rodneyknaap/atx-turboxt-v3/Turbo_XT_Mainboard R3.sch

## KiCad design Turbo_XT_Mainboard R3.sch (2023-07-02)

Schematic: Turbo_XT_Mainboard R3.sch

Parts:
C1: 50p; Trimmer_C
C2, C3: 12p; C_Disc_D3.8mm_W2.6mm_P2.50mm
C4: 100n; C_Disc_D5.0mm_W2.5mm_P5.00mm
C5, C6, C7: 1nF; C_Disc_D3.8mm_W2.6mm_P2.50mm
C8, C14, C15, C16, C17, C18, C30, C31, C32, C33, C34, C35, C36, C37, C38, C39, C40, C41, C42, C43, C44, C45, C46, C47, C48, C49, C50, C51, C52, C53, C54, C55, C56, C57, C58, C59, C60, C61, C62, C63, C64, C65, C66, C67, C68, C69, C70, C71, C72, C73, C74, C75, C76, C77, C78, C79, C80, C81, C82, C83, C84, C85, C89, C90, C91, C92, C93, C94, C95, C96, C97, C99, C151, C177, C179, C181, C183, C184, C186, C187: 100nF; C_Rect_L7.0mm_W2.0mm_P5.00mm
C9, C10, C87, C88: 22pF; C_Disc_D3.8mm_W2.6mm_P2.50mm
C11: 4,7uF; CP_Radial_D4.0mm_P2.00mm
C12, C13: 100nF; C_Disc_D4.7mm_W2.5mm_P5.00mm
C21, C22, C23, C24, C25, C26, C27, C28, C29: 2,2nF; C_Disc_D4.7mm_W2.5mm_P5.00mm
C86, C178, C180: 1000µF; CP_Radial_D10.0mm_P5.00mm
C98: 2n2; C_Disc_D3.8mm_W2.6mm_P2.50mm
C100, C152, C188: 100µF; CP_Radial_D8.0mm_P3.80mm
C101, C102, C103, C105, C106, C107, C108, C109, C110, C111, C112, C114, C115, C116, C117, C118, C119, C120, C121, C122, C123, C124, C125, C126, C127, C128, C129, C130, C131, C132, C133, C134, C135, C136, C137, C138, C139, C140, C141, C142, C143, C144, C145, C146, C147, C148, C149, C150, C155, C156, C157, C158, C159, C160, C161, C162, C163, C164, C165, C166, C167, C168, C169, C170, C171, C172, C173, C174, C175, C176: 470p; C_Disc_D3.8mm_W2.6mm_P2.50mm
C104: 150p; C_Disc_D3.8mm_W2.6mm_P2.50mm
C113: 100p; C_Disc_D3.8mm_W2.6mm_P2.50mm
C153, C154: 1n; C_Disc_D3.8mm_W2.6mm_P2.50mm
C182: 47pF; C_Rect_L7.0mm_W2.0mm_P5.00mm
C185: 10µF; CP_Radial_D6.3mm_P2.50mm
D1: 1N4148; D_DO-35_SOD27_P5.08mm_Horizontal
D2: LED; LED_D5.0mm
D4: 1N5819; D_DO-15_P10.16mm_Horizontal
F1: FUSE 8A; R_Axial_DIN0207_L6.3mm_D2.5mm_P10.16mm_Horizontal
F2: FUSE 5A; R_Axial_DIN0207_L6.3mm_D2.5mm_P10.16mm_Horizontal
F3: FUSE 1A; R_Axial_DIN0207_L6.3mm_D2.5mm_P10.16mm_Horizontal
FB1: Ferrite_Bead_Small; R_Axial_DIN0207_L6.3mm_D2.5mm_P10.16mm_Horizontal
H1, H2, H3, H4, H5, H6, H7, H8, H9, H10: MountingHole_Pad; MountingHole_4mm_Pad_Via
J1: SPEAKER; PinHeader_1x04_P2.54mm_Vertical
J2, J4, J15, J17, J19, J23, J24: Conn_01x02; PinHeader_1x02_P2.54mm_Vertical
J5: Conn_01x05_Shielded; DIN_5P_FEMALE_PCB
J6, J8, J9, J10, J11, J12, J13: ISA_16bit_Slot; PCB_edge_ISA_Slot
J14: ATX-24 PSU; Molex_Mini-Fit_Jr_5566-24A2_2x12_P4.20mm_Vertical
J18: Conn_02x17_Odd_Even; IDC-Header_2x17_P2.54mm_Vertical
J20: Conn_01x25_Shielded_LPT; DSUB-25_Female_Horizontal_P2.77x2.84mm_EdgePinOffset4.94mm_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
J21: IDE_BUS; IDC-Header_2x20_P2.54mm_Vertical
J22: HDD_ACT_LED; PinHeader_1x02_P2.54mm_Vertical
J25: Conn_01x09_Shielded; DSUB-9_Male_Horizontal_COMPORT
J28: RJ45_Hanrun_HR911105A
J30, J31, J32: Conn_01x03; PinHeader_1x03_P2.54mm_Vertical
J33: SCSI_ADDRESS; PinHeader_2x03_P2.54mm_Vertical
J36: SCSI_INTERNAL; IDC-Header_2x25_P2.54mm_Vertical
Q1: 2N4401; TO-92_Wide
R4, R32, R35, R38, R39, R40, R43, R44: 10k; R_Axial_DIN0207_L6.3mm_D2.5mm_P10.16mm_Horizontal
R8, R27, R30, R48, R49: 4k7; R_Axial_DIN0207_L6.3mm_D2.5mm_P10.16mm_Horizontal
R9, R10: 510; R_Axial_DIN0207_L6.3mm_D2.5mm_P10.16mm_Horizontal
R11, R25, R45: 10M; R_Axial_DIN0207_L6.3mm_D2.5mm_P10.16mm_Horizontal
R12: 270; R_Axial_DIN0207_L6.3mm_D2.5mm_P10.16mm_Horizontal
R14, R42: 1k; R_Axial_DIN0207_L6.3mm_D2.5mm_P10.16mm_Horizontal
R15: 10; R_Axial_DIN0207_L6.3mm_D2.5mm_P10.16mm_Horizontal
R16, R36: 470; R_Axial_DIN0207_L6.3mm_D2.5mm_P10.16mm_Horizontal
R19, R20, R21, R22, R23: 33; R_Axial_DIN0207_L6.3mm_D2.5mm_P10.16mm_Horizontal
R26, R46: 2k2; R_Axial_DIN0207_L6.3mm_D2.5mm_P10.16mm_Horizontal
R28, R31: 100k; R_Axial_DIN0207_L6.3mm_D2.5mm_P10.16mm_Horizontal
R50: 27k; R_Axial_DIN0207_L6.3mm_D2.5mm_P10.16mm_Horizontal
R51: 200; R_Axial_DIN0207_L6.3mm_D2.5mm_P10.16mm_Horizontal
R52, R53: 330; R_Axial_DIN0207_L6.3mm_D2.5mm_P10.16mm_Horizontal
R56, R58: 220; R_Axial_DIN0207_L6.3mm_D2.5mm_P7.62mm_Horizontal
R57, R59: 330; R_Axial_DIN0207_L6.3mm_D2.5mm_P7.62mm_Horizontal
RN1, RN2: 8x 4k7; R_Array_SIP9
RN3: 4x 4k7; R_Array_SIP5
RN4: 4k7 x 8; R_Array_SIP9
RN5: 1kx8; R_Array_SIP9
RN6: 4k7x8; R_Array_SIP9
RN7, RN9: 8x 220; R_Array_SIP9
RN8, RN10: 8x 330; R_Array_SIP9
RN11: 8x 10k; R_Array_SIP9
SW1: SW_DIP_x08; SW_DIP_SPSTx08_Slide_9.78x22.5mm_W7.62mm_P2.54mm
U1: D70108C-8 NEC V20; DIP-40_W15.24mm
U2, U4, U24, U74, U75: 74HCT573E TI; DIP-20_W7.62mm
U3, U5, U6, U7, U8, U9, U10, U17: 74LS245N TI; DIP-20_W7.62mm
U12: TMS27C010A TI; DIP-32_W15.24mm
U13, U14: K6T4008CTB; DIP-32_W15.24mm
U15: 8087; DIP-40_W15.24mm
U16: CP82C88 HARRIS; DIP-20_W7.62mm
U19: M82C84A-2 OKI; DIP-18_W7.62mm
U20: 74HCT04N PHI; DIP-14_W7.62mm
U21: 74LS92N; DIP-14_W7.62mm
U22: D8237AC-5 NEC 1984; DIP-40_W15.24mm
U23: 74LS670N TI; DIP-16_W7.62mm
U25: 74LS138N TI; DIP-16_W7.62mm
U26: D8253C-2 NEC; DIP-24_W15.24mm
U27: D71055C NEC; DIP-40_W15.24mm
U28: 74LS322AN; DIP-20_W7.62mm
U29: 74LS244N TI; DIP-20_W7.62mm
U30, U31: D8259AC-2 NEC; DIP-28_W15.24mm
U32: GM82C765B LGS; DIP-40_W15.24mm
U33, U78, U83, U84: 74LS138N; DIP-16_W7.62mm
U34: 74LS125AN TI; DIP-14_W7.62mm
U36: 74LS32N; DIP-14_W7.62mm
U37, U79: 74LS04N TI; DIP-14_W7.62mm
U38: NE555P; DIP-8_W7.62mm
U39, U56, U58, U60, U62, U96: 74HCT74E RCA; DIP-14_W7.62mm
U40, U41: CD4020BE TI; DIP-16_W7.62mm
U43, U47, U76, U100: 74HCT245N TI; DIP-20_W7.62mm
U44, U85: 74HCT139N PHI; DIP-16_W7.62mm
U45: 74LS174N TI; DIP-16_W7.62mm
U46: 74HCT574N TI; DIP-20_W7.62mm
U48, U86, U90: 74HCT32N; DIP-14_W7.62mm
U49, U66: 74LS06N TI; DIP-14_W7.62mm
U54, U71, U95: 74HCT04N; DIP-14_W7.62mm
U55: 74HC08 PHI; DIP-14_W7.62mm
U59: 74HCT00 PHI; DIP-14_W7.62mm
U61, U89: 74HC08N PHI; DIP-14_W7.62mm
U64, U65: 74LS74AN; DIP-14_W7.62mm
U68, U69, U70: 74LS125AN MOT; DIP-14_W7.62mm
U73: 74LS245 TI; DIP-20_W7.62mm
U80: 74HCT04; DIP-14_W7.62mm
U81: 74LS32N TI; DIP-14_W7.62mm
U87: 73LS138N; DIP-16_W7.62mm
U88: 74HC08N TI; DIP-14_W7.62mm
U91: GM16C550 LGS; DIP-40_W15.24mm
U93: GD75232 TI; DIP-20_W7.62mm
U97: RTL8019AS; PQFP-100_14x20mm_P0.65mm_wider_pads_26,20x20,00_PCB
U98: HT93LC46; DIP-8_W7.62mm
U99: 53C400 NCR; PLCC-68_Extended
Y1: 14.31818 Mhz; Crystal_HC49-4H_Vertical
Y2: 24 Mhz; Crystal_HC49-4H_Vertical
Y3: 16Mhz; Crystal_HC49-4H_Vertical
Y4: 7.3728 Mhz; Crystal_HC49-4H_Vertical
Y5: 20 Mhz; Crystal_HC49-4H_Vertical

Connections:
1.8432M: U91.16 (XIN), U96.9 (Q)
5VSB: C14.1, C15.1, C16.1, C17.1, C18.1, C78.1, D2.2 (A), J14.9 (+5VSB), J15.1, J17.1, R32.1, U36.9, U36.10, U36.12, U36.13, U36.14 (VCC), U37.14 (VCC), U38.4 (R), U38.8 (VCC), U39.4 (~S), U39.10 (~S), U39.14 (VCC), U40.16 (VDD), U41.16 (VDD)
12V: C187.1, C188.1, F2.1, J6.9 (+12V), J8.9 (+12V), J9.9 (+12V), J10.9 (+12V), J11.9 (+12V), J12.9 (+12V), J13.9 (+12V), U93.1 (VDD)
24M: U19.14 (EFI), U20.4
-5V: C151.1, C152.2, J6.5 (-5V), J8.5 (-5V), J9.5 (-5V), J10.5 (-5V), J11.5 (-5V), J12.5 (-5V), J13.5 (-5V), J32.3
-12V: C99.1, C100.2, J6.7 (-12V), J8.7 (-12V), J9.7 (-12V), J10.7 (-12V), J11.7 (-12V), J12.7 (-12V), J13.7 (-12V), J14.14 (-12V), J32.1, U93.10 (VSS)
A0: C130.1, J6.62 (BA00), J8.62 (BA00), J9.62 (BA00), J10.62 (BA00), J11.62 (BA00), J12.62 (BA00), J13.62 (BA00), U4.12 (Q7), U6.9 (A7), U76.2 (A0), U99.26 (A0)
A1: C131.1, J6.61 (BA01), J8.61 (BA01), J9.61 (BA01), J10.61 (BA01), J11.61 (BA01), J12.61 (BA01), J13.61 (BA01), U4.13 (Q6), U6.8 (A6), U76.3 (A1), U99.27 (A1)
A2: C132.1, J6.60 (BA02), J8.60 (BA02), J9.60 (BA02), J10.60 (BA02), J11.60 (BA02), J12.60 (BA02), J13.60 (BA02), U4.14 (Q5), U6.7 (A5), U76.4 (A2), U99.28 (A2)
A3: C133.1, J6.59 (BA03), J8.59 (BA03), J9.59 (BA03), J10.59 (BA03), J11.59 (BA03), J12.59 (BA03), J13.59 (BA03), U4.15 (Q4), U6.6 (A4), U76.5 (A3), U99.29 (A3)
A4: C134.1, J6.58 (BA04), J8.58 (BA04), J9.58 (BA04), J10.58 (BA04), J11.58 (BA04), J12.58 (BA04), J13.58 (BA04), U4.16 (Q3), U6.5 (A3), U84.1 (A0), U97.10 (A4), U99.30 (A4)
A5: C135.1, J6.57 (BA05), J8.57 (BA05), J9.57 (BA05), J10.57 (BA05), J11.57 (BA05), J12.57 (BA05), J13.57 (BA05), U4.17 (Q2), U6.4 (A2), U84.2 (A1), U97.11 (A5), U99.31 (A5)
A6: C136.1, J6.56 (BA06), J8.56 (BA06), J9.56 (BA06), J10.56 (BA06), J11.56 (BA06), J12.56 (BA06), J13.56 (BA06), U4.18 (Q1), U6.3 (A1), U84.3 (A2), U97.12 (A6), U99.32 (A6)
A7: C137.1, J6.55 (BA07), J8.55 (BA07), J9.55 (BA07), J10.55 (BA07), J11.55 (BA07), J12.55 (BA07), J13.55 (BA07), U4.19 (Q0), U6.2 (A0), U83.1 (A0), U97.13 (A7), U99.33 (A7)
A8: C138.1, J6.54 (BA08), J8.54 (BA08), J9.54 (BA08), J10.54 (BA08), J11.54 (BA08), J12.54 (BA08), J13.54 (BA08), U3.2 (A0), U7.9 (A7), U24.12 (Q7), U83.2 (A1), U97.15 (A8), U99.34 (A8)
A9: C139.1, J6.53 (BA09), J8.53 (BA09), J9.53 (BA09), J10.53 (BA09), J11.53 (BA09), J12.53 (BA09), J13.53 (BA09), U3.3 (A1), U7.8 (A6), U24.13 (Q6), U83.3 (A2), U97.16 (A9), U99.35 (A9)
A10: C140.1, J6.52 (BA10), J8.52 (BA10), J9.52 (BA10), J10.52 (BA10), J11.52 (BA10), J12.52 (BA10), J13.52 (BA10), U3.4 (A2), U7.7 (A5), U24.14 (Q5), U99.36 (A10)
A11: C141.1, J6.51 (BA11), J8.51 (BA11), J9.51 (BA11), J10.51 (BA11), J11.51 (BA11), J12.51 (BA11), J13.51 (BA11), U3.5 (A3), U7.6 (A4), U24.15 (Q4), U99.37 (A11)
A12: C142.1, J6.50 (BA12), J8.50 (BA12), J9.50 (BA12), J10.50 (BA12), J11.50 (BA12), J12.50 (BA12), J13.50 (BA12), U2.17 (Q2), U7.5 (A3), U24.16 (Q3), U99.38 (A12)
A13: C143.1, J6.49 (BA13), J8.49 (BA13), J9.49 (BA13), J10.49 (BA13), J11.49 (BA13), J12.49 (BA13), J13.49 (BA13), U2.15 (Q4), U7.4 (A2), U24.17 (Q2), U99.39 (A13)
A14: C144.1, J6.48 (BA14), J8.48 (BA14), J9.48 (BA14), J10.48 (BA14), J11.48 (BA14), J12.48 (BA14), J13.48 (BA14), U2.13 (Q6), U7.3 (A1), U24.18 (Q1), U99.40 (A14)
A15: C145.1, J6.47 (BA15), J8.47 (BA15), J9.47 (BA15), J10.47 (BA15), J11.47 (BA15), J12.47 (BA15), J13.47 (BA15), U2.12 (Q7), U7.2 (A0), U24.19 (Q0), U99.41 (A15)
A16: C146.1, J6.46 (BA16), J8.46 (BA16), J9.46 (BA16), J10.46 (BA16), J11.46 (BA16), J12.46 (BA16), J13.46 (BA16), U2.14 (Q5), U8.2 (A0), U23.10 (Q1), U99.42 (A16)
A17: C147.1, J6.45 (BA17), J8.45 (BA17), J9.45 (BA17), J10.45 (BA17), J11.45 (BA17), J12.45 (BA17), J13.45 (BA17), U2.16 (Q3), U8.3 (A1), U23.9 (Q2), U99.43 (A17)
A18: C148.1, J6.44 (BA18), J8.44 (BA18), J9.44 (BA18), J10.44 (BA18), J11.44 (BA18), J12.44 (BA18), J13.44 (BA18), U2.18 (Q1), U8.4 (A2), U23.7 (Q3), U99.44 (A18)
A19: C149.1, J6.43 (BA19), J8.43 (BA19), J9.43 (BA19), J10.43 (BA19), J11.43 (BA19), J12.43 (BA19), J13.43 (BA19), U2.19 (Q0), U8.5 (A3), U23.6 (Q4), U89.4, U99.45 (A19)
AA8: U1.8 (A8), U3.18 (B0), U15.8 (AD8)
AA9: U1.7 (A9), U3.17 (B1), U15.7 (AD9)
AA10: U1.6 (A10), U3.16 (B2), U15.6 (AD10)
AA11: U1.5 (A11), U3.15 (B3), U15.5 (AD11)
AA12: U1.4 (A12), U2.4 (D2), U15.4 (AD12)
AA13: U1.3 (A13), U2.6 (D4), U15.3 (AD13)
AA14: U1.2 (A14), U2.8 (D6), U15.2 (AD14)
AA15: U1.39 (A15), U2.9 (D7), U15.39 (AD15)
AA16: U1.38 (A16/S3), U2.7 (D5), U15.38 (A16/S3)
AA17: U1.37 (A17/S4), U2.5 (D3), U15.37 (A17/S4)
AA18: U1.36 (A18/S5), U2.3 (D1), U15.36 (A18/S5)
AA19: U1.35 (A19/S6), U2.2 (D0), U15.35 (A19/S6)
AD0: U1.16 (AD0), U4.9 (D7), U5.9 (A7), U15.16 (AD0)
AD1: U1.15 (AD1), U4.8 (D6), U5.8 (A6), U15.15 (AD1)
AD2: U1.14 (AD2), U4.7 (D5), U5.7 (A5), U15.14 (AD2)
AD3: U1.13 (AD3), U4.6 (D4), U5.6 (A4), U15.13 (AD3)
AD4: U1.12 (AD4), U4.5 (D3), U5.5 (A3), U15.12 (AD4)
AD5: U1.11 (AD5), U4.4 (D2), U5.4 (A2), U15.11 (AD5)
AD6: U1.10 (AD6), U4.3 (D1), U5.3 (A1), U15.10 (AD6)
AD7: U1.9 (AD7), U4.2 (D0), U5.2 (A0), U15.9 (AD7)
AEN: C105.2, J6.42 (AEN), J8.42 (AEN), J9.42 (AEN), J10.42 (AEN), J11.42 (AEN), J12.42 (AEN), J13.42 (AEN), U8.12 (B6), U83.4 (E1), U97.34 (AEN), U99.25 (AEN)
AENBRD: U2.1 (OE), U3.19 (CE), U4.1 (OE), U8.8 (A6), U9.19 (CE), U16.6 (~AEN~), U58.5 (Q), U59.4, U60.12 (D), U61.4
ALE: C121.2, J6.28 (ALE), J8.28 (ALE), J9.28 (ALE), J10.28 (ALE), J11.28 (ALE), J12.28 (ALE), J13.28 (ALE), U2.11 (Load), U4.11 (Load), U16.5 (ALE)
BA0: U32.4 (A0), U44.2 (A0), U44.14 (A0), U76.18 (B0), U78.3 (A2), U85.14 (A0), U91.28 (A0), U97.5 (A0)
BA1: J21.33, U33.1 (A0), U44.3 (A1), U44.13 (A1), U76.17 (B1), U79.5, U91.27 (A1), U97.7 (A1)
BA2: J21.36, U33.2 (A1), U76.16 (B2), U85.2 (A0), U91.26 (A2), U97.8 (A2)
BA3: J21.35, U33.3 (A2), U76.15 (B3), U85.3 (A1), U91.12 (CS0), U97.9 (A3)
CLK: C113.2, J6.20 (CLK), J8.20 (CLK), J9.20 (CLK), J10.20 (CLK), J11.20 (CLK), J12.20 (CLK), J13.20 (CLK), U8.14 (B4), U54.9, U56.3 (C), U58.3 (C), U60.3 (C), U60.11 (C), U99.23 (CLK)
COM1_CTS: J25.8, U93.7 (RA4)
COM1_DCD: J25.1, U93.2 (RA1)
COM1_DSR: J25.6, U93.3 (RA2)
COM1_DTR: J25.4, U93.8 (DY3)
COM1_RI: J25.9, U93.9 (RA5)
COM1_RTS: J25.7, U93.5 (DY1)
COM1_RX: J25.2, U93.4 (RA3)
COM1_SIN: U91.10 (SIN), U93.17 (RY3)
COM1_SOUT: U91.11 (SOUT), U93.15 (DA2)
COM1_TX: J25.3, U93.6 (DY2)
CPU_CLK: R22.2, U1.19 (CLK), U8.6 (A4), U15.19 (CLK), U16.2 (CLK)
D0: C122.1, J6.40 (DB0), J8.40 (DB0), J9.40 (DB0), J10.40 (DB0), J11.40 (DB0), J12.40 (DB0), J13.40 (DB0), RN11.9 (R8), U5.11 (B7), U9.2 (A0), U10.2 (A0), U32.7 (DB0), U43.2 (A0), U73.2 (A0), U91.1 (D0), U97.36 (D0), U100.2 (A0)
D1: C123.1, J6.39 (DB1), J8.39 (DB1), J9.39 (DB1), J10.39 (DB1), J11.39 (DB1), J12.39 (DB1), J13.39 (DB1), RN11.8 (R7), U5.12 (B6), U9.3 (A1), U10.3 (A1), U32.8 (DB1), U43.3 (A1), U73.3 (A1), U91.2 (D1), U97.37 (D1), U100.3 (A1)
D2: C124.1, J6.38 (DB2), J8.38 (DB2), J9.38 (DB2), J10.38 (DB2), J11.38 (DB2), J12.38 (DB2), J13.38 (DB2), RN11.7 (R6), U5.13 (B5), U9.4 (A2), U10.4 (A2), U32.9 (DB2), U43.4 (A2), U73.4 (A2), U91.3 (D2), U97.38 (D2), U100.4 (A2)
D3: C125.1, J6.37 (DB3), J8.37 (DB3), J9.37 (DB3), J10.37 (DB3), J11.37 (DB3), J12.37 (DB3), J13.37 (DB3), RN11.6 (R5), U5.14 (B4), U9.5 (A3), U10.5 (A3), U32.10 (DB3), U43.5 (A3), U73.5 (A3), U91.4 (D3), U97.39 (D3), U100.5 (A3)
D4: C126.1, J6.36 (DB4), J8.36 (DB4), J9.36 (DB4), J10.36 (DB4), J11.36 (DB4), J12.36 (DB4), J13.36 (DB4), RN11.5 (R4), U5.15 (B3), U9.6 (A4), U10.6 (A4), U32.11 (DB4), U43.6 (A4), U73.6 (A4), U91.5 (D4), U97.40 (D4), U100.6 (A4)
D5: C127.1, J6.35 (DB5), J8.35 (DB5), J9.35 (DB5), J10.35 (DB5), J11.35 (DB5), J12.35 (DB5), J13.35 (DB5), RN11.4 (R3), U5.16 (B2), U9.7 (A5), U10.7 (A5), U32.12 (DB5), U43.7 (A5), U73.7 (A5), U91.6 (D5), U97.41 (D5), U100.7 (A5)
D6: C128.1, J6.34 (DB6), J8.34 (DB6), J9.34 (DB6), J10.34 (DB6), J11.34 (DB6), J12.34 (DB6), J13.34 (DB6), RN11.3 (R2), U5.17 (B1), U9.8 (A6), U10.8 (A6), U32.13 (DB6), U43.8 (A6), U73.8 (A6), U91.7 (D6), U97.42 (D6), U100.8 (A6)
D7: C129.1, J6.33 (DB7), J8.33 (DB7), J9.33 (DB7), J10.33 (DB7), J11.33 (DB7), J12.33 (DB7), J13.33 (DB7), RN11.2 (R1), U5.18 (B0), U9.9 (A7), U10.9 (A7), U32.14 (DB7), U34.6, U43.9 (A7), U73.9 (A7), U91.8 (D7), U97.43 (D7), U100.9 (A7)
D8: C169.1, J6.91 (D8), J8.91 (D8), J9.91 (D8), J10.91 (D8), J11.91 (D8), J12.91 (D8), J13.91 (D8)
D9: C170.1, J6.92 (D9), J8.92 (D9), J9.92 (D9), J10.92 (D9), J11.92 (D9), J12.92 (D9), J13.92 (D9)
D10: C171.1, J6.93 (D10), J8.93 (D10), J9.93 (D10), J10.93 (D10), J11.93 (D10), J12.93 (D10), J13.93 (D10)
D11: C172.1, J6.94 (D11), J8.94 (D11), J9.94 (D11), J10.94 (D11), J11.94 (D11), J12.94 (D11), J13.94 (D11)
D12: C173.1, J6.95 (D12), J8.95 (D12), J9.95 (D12), J10.95 (D12), J11.95 (D12), J12.95 (D12), J13.95 (D12)
D13: C174.1, J6.96 (D13), J8.96 (D13), J9.96 (D13), J10.96 (D13), J11.96 (D13), J12.96 (D13), J13.96 (D13)
D14: C175.1, J6.97 (D14), J8.97 (D14), J9.97 (D14), J10.97 (D14), J11.97 (D14), J12.97 (D14), J13.97 (D14)
D15: C176.1, J6.98 (D15), J8.98 (D15), J9.98 (D15), J10.98 (D15), J11.98 (D15), J12.98 (D15), J13.98 (D15)
DEN: U16.16 (DEN), U54.13
DENSEL: J18.2, U32.36 (~RWC~_~RPM)
DMACLK: U22.12 (CLK), U62.11 (C), U86.3
DMA_ADSTB: U22.8 (ADSTB), U24.11 (Load)
DRQ0: U22.19 (DREQ0)
DRQ1: C111.2, J6.18 (DRQ1), J8.18 (DRQ1), J9.18 (DRQ1), J10.18 (DRQ1), J11.18 (DRQ1), J12.18 (DRQ1), J13.18 (DRQ1), U22.18 (DREQ1)
DRQ2: C102.2, J6.6 (DRQ2), J8.6 (DRQ2), J9.6 (DRQ2), J10.6 (DRQ2), J11.6 (DRQ2), J12.6 (DRQ2), J13.6 (DRQ2), U22.17 (DREQ2), U32.15 (DMA)
DRQ3: C109.2, J6.16 (DRQ3), J8.16 (DRQ3), J9.16 (DRQ3), J10.16 (DRQ3), J11.16 (DRQ3), J12.16 (DRQ3), J13.16 (DRQ3), U22.16 (DREQ3)
DSW1: RN2.9 (R8), SW1.1, U29.2 (I0a)
DSW2: RN2.8 (R7), SW1.2, U29.4 (I1a)
DSW3: RN2.7 (R6), SW1.3, U29.6 (I2a)
DSW4: RN2.6 (R5), SW1.4, U29.8 (I3a)
DSW5: RN2.5 (R4), SW1.5, U29.11 (I0b)
DSW6: RN2.4 (R3), SW1.6, U29.13 (I1b)
DSW7: RN2.3 (R2), SW1.7, U29.15 (I2b)
DSW8: RN2.2 (R1), SW1.8, U29.17 (I3b)
DT_~R: U5.1 (A->B), U16.4 (DT/~R~)
FDC_CLK: U20.10, U32.23 (CLK1)
GNDD: C2.1, C3.2, C4.2, C5.2, C6.2, C7.2, C8.2, C9.1, C10.2, C11.2, C12.2, C13.2, C14.2, C15.2, C16.2, C17.2, C18.2, C21.2, C22.2, C23.2, C24.2, C25.2, C26.2, C27.2, C28.2, C29.2, C30.2, C31.2, C32.2, C33.2, C34.2, C35.2, C36.2, C37.2, C38.2, C39.2, C40.2, C41.2, C42.2, C43.2, C44.2, C45.2, C46.2, C47.2, C48.2, C49.2, C50.2, C51.2, C52.2, C53.2, C54.2, C55.2, C56.2, C57.2, C58.2, C59.2, C60.2, C61.2, C62.2, C63.2, C64.2, C65.2, C66.2, C67.2, C68.2, C69.2, C70.2, C71.2, C72.2, C73.2, C74.2, C75.2, C76.2, C77.2, C78.2, C79.2, C80.2, C81.2, C82.2, C83.2, C84.2, C85.2, C86.2, C87.1, C88.2, C89.2, C90.2, C91.2, C92.2, C93.2, C94.2, C95.2, C96.2, C97.2, C98.1, C99.2, C100.1, C101.1, C102.1, C103.1, C104.1, C105.1, C106.1, C107.1, C108.1, C109.1, C110.1, C111.1, C112.1, C113.1, C114.1, C115.1, C116.1, C117.1, C118.1, C119.1, C120.1, C121.1, C122.2, C123.2, C124.2, C125.2, C126.2, C127.2, C128.2, C129.2, C130.2, C131.2, C132.2, C133.2, C134.2, C135.2, C136.2, C137.2, C138.2, C139.2, C140.2, C141.2, C142.2, C143.2, C144.2, C145.2, C146.2, C147.2, C148.2, C149.2, C150.1, C151.2, C152.1, C153.1, C154.1, C155.1, C156.1, C157.1, C158.1, C159.1, C160.1, C161.1, C162.1, C163.1, C164.1, C165.1, C166.1, C167.1, C168.1, C169.2, C170.2, C171.2, C172.2, C173.2, C174.2, C175.2, C176.2, C177.2, C178.2, C179.2, C180.2, C181.2, C183.2, C184.2, C185.2, C186.2, C187.2, C188.2, H1.1, H2.1, H3.1, H4.1, H5.1, H6.1, H7.1, H8.1, H9.1, H10.1, J1.3, J5.4, J5.SH (Shield), J6.1 (GND), J6.10 (GND), J6.31 (GND), J6.80 (GND), J8.1 (GND), J8.10 (GND), J8.31 (GND), J8.80 (GND), J9.1 (GND), J9.10 (GND), J9.31 (GND), J9.80 (GND), J10.1 (GND), J10.10 (GND), J10.31 (GND), J10.80 (GND), J11.1 (GND), J11.10 (GND), J11.31 (GND), J11.80 (GND), J12.1 (GND), J12.10 (GND), J12.31 (GND), J12.80 (GND), J13.1 (GND), J13.10 (GND), J13.31 (GND), J13.80 (GND), J14.3 (GND), J14.5 (GND), J14.7 (GND), J14.15 (GND), J14.17 (GND), J14.18 (GND), J14.19 (GND), J14.24 (GND), J18.1, J18.3, J18.5, J18.7, J18.9, J18.11, J18.13, J18.15, J18.17, J18.19, J18.21, J18.23, J18.25, J18.27, J18.29, J18.31, J18.33, J20.0 (Shield), J20.18, J20.19, J20.20, J20.21, J20.22, J20.23, J20.24, J20.25, J21.2, J21.19, J21.22, J21.24, J21.26, J21.28, J21.30, J21.40, J25.5, J25.SH (Shield), J28.8 (GND), J28.SH (SHIELD), J31.3, J32.2, J33.2, J33.4, J33.6, J36.1, J36.3, J36.5, J36.7, J36.9, J36.11, J36.13, J36.15, J36.17, J36.19, J36.20, J36.21, J36.22, J36.23, J36.24, J36.27, J36.28, J36.29, J36.30, J36.31, J36.33, J36.34, J36.35, J36.37, J36.39, J36.41, J36.43, J36.45, J36.47, J36.49, Q1.1 (E), R4.1, R8.1, R9.1, R10.2, R28.1, R31.1, R36.2, R39.2, R40.2, R50.2, R57.1, R59.1, RN8.1 (common), RN10.1 (common), SW1.9, SW1.10, SW1.11, SW1.12, SW1.13, SW1.14, SW1.15, SW1.16, U1.1 (GND), U1.20 (GND), U1.33 (MN/~MX~), U2.10 (GND), U3.1 (A->B), U3.10 (GND), U4.10 (GND), U5.10 (GND), U6.10 (GND), U7.10 (GND), U7.19 (CE), U8.10 (GND), U8.19 (CE), U9.10 (GND), U10.10 (GND), U12.16 (GND), U13.16 (VSS), U14.16 (VSS), U15.1 (GND), U15.20 (GND), U16.1 (IOB), U16.10 (GND), U17.10 (GND), U17.19 (CE), U19.1 (CSYNC), U19.6 (RDY2), U19.9 (GND), U19.15 (~ASYNC~), U20.5, U20.7 (GND), U20.9, U21.10 (GND), U22.20 (Vss), U23.8 (GND), U24.10 (GND), U25.8 (GND), U26.12 (GND), U27.7 (GND), U28.10 (GND), U29.10 (GND), U30.14 (GND), U31.14 (GND), U31.16 (~SP~/~EN~), U32.21 (CLK2), U32.22 (DRV), U32.31 (GND), U33.8 (GND), U34.2, U34.7 (GND), U36.7 (GND), U37.7 (GND), U37.9, U37.11, U37.13, U38.1 (GND), U39.7 (GND), U39.11 (C), U39.12 (D), U39.13 (~R), U40.8 (VSS), U41.8 (VSS), U43.10 (GND), U43.19 (CE), U44.8 (GND), U45.8 (GND), U46.10 (GND), U47.10 (GND), U48.7 (GND), U49.7 (GND), U54.1, U54.7 (GND), U55.1, U55.2, U55.7 (GND), U56.7 (GND), U58.7 (GND), U59.7 (GND), U59.9, U59.10, U59.12, U59.13, U60.7 (GND), U61.7 (GND), U62.7 (GND), U64.7 (GND), U65.7 (GND), U65.13 (~R), U66.7 (GND), U66.13, U68.7 (GND), U69.7 (GND), U70.1, U70.7 (GND), U71.7 (GND), U71.9, U73.10 (GND), U74.10 (GND), U75.10 (GND), U76.10 (GND), U76.19 (CE), U78.8 (GND), U79.7 (GND), U79.11, U79.13, U80.7 (GND), U81.7 (GND), U81.13, U83.5 (E2), U83.8 (GND), U84.4 (E1), U84.5 (E2), U84.8 (GND), U85.1 (E), U85.8 (GND), U85.13 (A1), U86.7 (GND), U87.4 (E1), U87.5 (E2), U87.8 (GND), U88.7 (GND), U89.7 (GND), U90.7 (GND), U91.19 (WR), U91.20 (GND), U91.22 (RD), U91.25 (~ADS~), U91.35 (MR), U93.11 (GND), U95.3, U95.5, U95.7 (GND), U95.9, U96.7 (GND), U97.14 (GND), U97.18 (A10), U97.19 (A11), U97.20 (A12), U97.21 (A13), U97.22 (A14), U97.23 (A15), U97.24 (A16), U97.25 (A17), U97.26 (A18), U97.27 (A19), U97.28 (GND), U97.44 (GND), U97.52 (GND), U97.64 (AUI), U97.83 (GND), U97.86 (GND), U98.5 (GND), U99.1 (GND), U99.18 (GND), U99.52 (GND), U99.58 (GND), U99.64 (GND), U100.10 (GND)
HOLDA: U22.7 (HLDA), U56.9 (Q), U58.2 (D)
HRQ_DMA: U22.10 (HRQ), U55.13, U56.13 (~R)
IDE_D0: J21.17, U73.18 (B0), U74.2 (D0), U75.19 (Q0)
IDE_D1: J21.15, U73.17 (B1), U74.3 (D1), U75.18 (Q1)
IDE_D2: J21.13, U73.16 (B2), U74.4 (D2), U75.17 (Q2)
IDE_D3: J21.11, U73.15 (B3), U74.5 (D3), U75.16 (Q3)
IDE_D4: J21.9, U73.14 (B4), U74.6 (D4), U75.15 (Q4)
IDE_D5: J21.7, U73.13 (B5), U74.7 (D5), U75.14 (Q5)
IDE_D6: J21.5, U73.12 (B6), U74.8 (D6), U75.13 (Q6)
IDE_D7: J21.3, R40.1, U73.11 (B7), U74.9 (D7), U75.12 (Q7)
IDE_D8: J21.4, U74.19 (Q0), U75.2 (D0)
IDE_D9: J21.6, U74.18 (Q1), U75.3 (D1)
IDE_D10: J21.8, U74.17 (Q2), U75.4 (D2)
IDE_D11: J21.10, U74.16 (Q3), U75.5 (D3)
IDE_D12: J21.12, U74.15 (Q4), U75.6 (D4)
IDE_D13: J21.14, U74.14 (Q5), U75.7 (D5)
IDE_D14: J21.16, U74.13 (Q6), U75.8 (D6)
IDE_D15: J21.18, U74.12 (Q7), U75.9 (D7)
INT: U1.18 (INTR), U30.17 (INT)
INTCAS0: U30.12 (CAS0), U31.12 (CAS0)
INTCAS1: U30.13 (CAS1), U31.13 (CAS1)
INTCAS2: U30.15 (CAS2), U31.15 (CAS2)
IOCHRDY: C150.2, J6.41 (IO_READY), J8.41 (IO_READY), J9.41 (IO_READY), J10.41 (IO_READY), J11.41 (IO_READY), J12.41 (IO_READY), J13.41 (IO_READY), RN1.8 (R7), U58.10 (~S), U97.35 (IOCHRDY)
IRQ0: U26.10 (OUT0), U30.18 (IR0)
IRQ1: U28.1 (G), U30.19 (IR1), U64.5 (Q), U66.3
IRQ2: U30.20 (IR2), U31.17 (INT)
IRQ3: C118.2, J6.25 (IRQ3), J8.25 (IRQ3), J9.25 (IRQ3), J10.25 (IRQ3), J11.25 (IRQ3), J12.25 (IRQ3), J13.25 (IRQ3), U30.21 (IR3), U97.3 (INT1)
IRQ4: C117.2, J6.24 (IRQ4), J8.24 (IRQ4), J9.24 (IRQ4), J10.24 (IRQ4), J11.24 (IRQ4), J12.24 (IRQ4), J13.24 (IRQ4), U30.22 (IR4), U91.30 (INTR)
IRQ5: C116.2, J6.23 (IRQ5), J8.23 (IRQ5), J9.23 (IRQ5), J10.23 (IRQ5), J11.23 (IRQ5), J12.23 (IRQ5), J13.23 (IRQ5), U30.23 (IR5)
IRQ6: C115.2, J6.22 (IRQ6), J8.22 (IRQ6), J9.22 (IRQ6), J10.22 (IRQ6), J11.22 (IRQ6), J12.22 (IRQ6), J13.22 (IRQ6), U30.24 (IR6), U32.16 (IRQ)
IRQ7: C114.2, J6.21 (IRQ7), J8.21 (IRQ7), J9.21 (IRQ7), J10.21 (IRQ7), J11.21 (IRQ7), J12.21 (IRQ7), J13.21 (IRQ7), J19.2, U30.25 (IR7), U99.4 (IRQ)
IRQ8: U31.18 (IR0)
IRQ9: C101.2, J6.4 (IRQ2), J8.4 (IRQ2), J9.4 (IRQ2), J10.4 (IRQ2), J11.4 (IRQ2), J12.4 (IRQ2), J13.4 (IRQ2), U31.19 (IR1)
IRQ10: C162.2, J6.65 (IRQ10), J8.65 (IRQ10), J9.65 (IRQ10), J10.65 (IRQ10), J11.65 (IRQ10), J12.65 (IRQ10), J13.65 (IRQ10), U31.20 (IR2)
IRQ11: C163.2, J6.66 (IRQ11), J8.66 (IRQ11), J9.66 (IRQ11), J10.66 (IRQ11), J11.66 (IRQ11), J12.66 (IRQ11), J13.66 (IRQ11), U31.21 (IR3)
IRQ12: C164.2, J6.67 (IRQ12), J8.67 (IRQ12), J9.67 (IRQ12), J10.67 (IRQ12), J11.67 (IRQ12), J12.67 (IRQ12), J13.67 (IRQ12), U31.22 (IR4)
IRQ13: U31.23 (IR5)
IRQ14: C165.2, J6.69 (IRQ14), J8.69 (IRQ14), J9.69 (IRQ14), J10.69 (IRQ14), J11.69 (IRQ14), J12.69 (IRQ14), J13.69 (IRQ14), U31.24 (IR6)
IRQ15: C166.2, J6.68 (IRQ15), J8.68 (IRQ15), J9.68 (IRQ15), J10.68 (IRQ15), J11.68 (IRQ15), J12.68 (IRQ15), J13.68 (IRQ15), U31.25 (IR7)
ISAIO: J6.32 (IO), J8.32 (IO), J9.32 (IO), J10.32 (IO), J11.32 (IO), J12.32 (IO), J13.32 (IO)
KBD_QH: U28.12 (Qh), U64.2 (D)
KB_CLK: C7.1, R19.1, RN6.4 (R3), U64.12 (D), U66.8
KB_DATA: C6.1, R20.1, RN6.2 (R1), U28.17 (D1), U66.4
LA17: C155.2, J6.88 (LA17), J8.88 (LA17), J9.88 (LA17), J10.88 (LA17), J11.88 (LA17), J12.88 (LA17), J13.88 (LA17)
LA18: C156.2, J6.87 (LA18), J8.87 (LA18), J9.87 (LA18), J10.87 (LA18), J11.87 (LA18), J12.87 (LA18), J13.87 (LA18)
LA19: C157.2, J6.86 (LA19), J8.86 (LA19), J9.86 (LA19), J10.86 (LA19), J11.86 (LA19), J12.86 (LA19), J13.86 (LA19)
LA20: C158.2, J6.85 (LA20), J8.85 (LA20), J9.85 (LA20), J10.85 (LA20), J11.85 (LA20), J12.85 (LA20), J13.85 (LA20)
LA21: C159.2, J6.84 (LA21), J8.84 (LA21), J9.84 (LA21), J10.84 (LA21), J11.84 (LA21), J12.84 (LA21), J13.84 (LA21)
LA22: C160.2, J6.83 (LA22), J8.83 (LA22), J9.83 (LA22), J10.83 (LA22), J11.83 (LA22), J12.83 (LA22), J13.83 (LA22)
LA23: C161.2, J6.82 (LA23), J8.82 (LA23), J9.82 (LA23), J10.82 (LA23), J11.82 (LA23), J12.82 (LA23), J13.82 (LA23)
LD0: U43.18 (B0), U45.3 (D0), U46.2 (D0), U47.18 (B0), U68.3
LD1: U43.17 (B1), U45.4 (D1), U46.3 (D1), U47.17 (B1), U70.8
LD2: U43.16 (B2), U45.6 (D2), U46.4 (D2), U47.16 (B2), U69.8
LD3: U43.15 (B3), U45.11 (D3), U46.5 (D3), U47.15 (B3), U68.6, U69.6
LD4: U43.14 (B4), U45.13 (D4), U46.6 (D4), U47.14 (B4), U68.8, U69.3
LD5: U43.13 (B5), U45.14 (D5), U46.7 (D5), U47.13 (B5), U68.11
LD6: U43.12 (B6), U46.8 (D6), U47.12 (B6), U69.11
LD7: U43.11 (B7), U46.9 (D7), U47.11 (B7), U70.11
LOAD_RD_H: U75.11 (Load), U79.2
LOAD_WR_H: U74.11 (Load), U79.4
LPT_ACK: U70.5, U71.2
LPT_AUTO_FD_XT: U70.9, U71.6
LPT_BUSY: J20.11, U71.13
LPT_D0: C21.1, J20.2, U46.19 (Q0), U47.2 (A0)
LPT_D1: C22.1, J20.3, U46.18 (Q1), U47.3 (A1)
LPT_D2: C23.1, J20.4, U46.17 (Q2), U47.4 (A2)
LPT_D3: C24.1, J20.5, U46.16 (Q3), U47.5 (A3)
LPT_D4: C25.1, J20.6, U46.15 (Q4), U47.6 (A4)
LPT_D5: C26.1, J20.7, U46.14 (Q5), U47.7 (A5)
LPT_D6: C27.1, J20.8, U46.13 (Q6), U47.8 (A6)
LPT_D7: C28.1, J20.9, U46.12 (Q7), U47.9 (A7)
LPT_EXT_DATA_IN: U45.15 (Q5), U46.1 (OE)
LPT_IRQ_EN: U45.12 (Q4), U49.9, U69.2
LPT_PE: J20.12, U68.12
LPT_SELECT: J20.13, U68.9
LPT_SELECT_IN: U69.5, U71.10
LPT_STROBE: U68.2, U71.4
MD0: U10.18 (B0), U13.13 (DQ0), U14.13 (DQ0)
MD1: U10.17 (B1), U13.14 (DQ1), U14.14 (DQ1)
MD2: U10.16 (B2), U13.15 (DQ2), U14.15 (DQ2)
MD3: U10.15 (B3), U13.17 (DQ3), U14.17 (DQ3)
MD4: U10.14 (B4), U13.18 (DQ4), U14.18 (DQ4)
MD5: U10.13 (B5), U13.19 (DQ5), U14.19 (DQ5)
MD6: U10.12 (B6), U13.20 (DQ6), U14.20 (DQ6)
MD7: U10.11 (B7), U13.21 (DQ7), U14.21 (DQ7)
NMI: R8.2, U1.17 (NMI)
NP_NPI: U15.32 (INT)
unnamed: C1.1, C182.1, R10.1, U19.17 (X1)
unnamed: C1.2, C182.2, Y1.2
unnamed: C2.2, R11.2, U20.1, Y2.1
unnamed: C3.1, R11.1, R12.2, Y2.2
unnamed: C4.1, Q1.3 (C), R15.2
unnamed: C8.1, FB1.1, J5.5
unnamed: C9.2, R25.2, U20.13, Y3.1
unnamed: C10.1, R25.1, R26.1, Y3.2
unnamed: C11.1, R32.2, U39.1 (~R)
unnamed: C12.1, R35.1, U38.2 (TR), U38.6 (THR)
unnamed: C13.1, U38.5 (CV)
unnamed: C87.2, R45.2, U95.13, Y4.1
unnamed: C88.1, R45.1, R46.1, Y4.2
unnamed: C153.2, J28.5 (RCT)
unnamed: C154.2, J28.4 (TCT)
unnamed: D1.1 (K), R27.2, R28.2, U41.11 (Reset)
unnamed: D2.1 (K), R36.1
unnamed: D4.1 (K), F3.1
unnamed: F1.2, J14.4 (+5V), J14.6 (+5V), J14.21 (+5V), J14.22 (+5V), J14.23 (+5V)
unnamed: F2.2, J14.10 (+12V)
unnamed: J1.1, R15.1
unnamed: J4.1, R16.2
unnamed: J4.2, U62.8 (~Q)
unnamed: J5.1, R19.2
unnamed: J5.2, R20.2
unnamed: J5.3, R21.2
unnamed: J14.16 (PS_ON#), U39.2 (D), U39.6 (~Q)
unnamed: J15.2, R30.1
unnamed: J17.2, R27.1
unnamed: J19.1, U70.6
unnamed: J22.1, R42.1
unnamed: J22.2, U34.3
unnamed: J23.1, R44.2, U88.9
unnamed: J23.2, U87.10 (O5)
unnamed: J24.1, R43.2, U88.10
unnamed: J24.2, U87.9 (O6)
unnamed: J28.1 (TD+), U97.45 (TPOUT+)
unnamed: J28.2 (TD-), U97.46 (TPOUT-)
unnamed: J28.3 (RD+), R51.1, U97.59 (TPIN+)
unnamed: J28.6 (RD-), R51.2, U97.58 (TPIN-)
unnamed: J28.9 (LEDG_A), R52.2
unnamed: J28.10 (LEDG_K), U97.61 (LED0)
unnamed: J28.11 (LEDY_K), U97.62 (LED1)
unnamed: J28.12 (LEDY_A), R53.2
unnamed: J30.2, U6.1 (A->B)
unnamed: J31.2, U6.19 (CE)
unnamed: Q1.2 (B), R14.1
unnamed: R9.2, U19.16 (X2), Y1.1
unnamed: R12.1, U20.2, U20.3
unnamed: R14.2, U88.11
unnamed: R22.1, U19.8 (CLK)
unnamed: R23.1, U19.12 (OSC)
unnamed: R26.2, U20.11, U20.12
unnamed: R30.2, R31.2, U40.11 (Reset)
unnamed: R46.2, U95.1, U95.12
unnamed: R49.2, U1.31 (~RQ~/~GT0~)
unnamed: R50.1, U97.96 (SLOT16)
unnamed: RN6.8 (R7), U49.6, U49.13
unnamed: U21.9 (Q2), U86.1
unnamed: U21.11 (Q1), U62.2 (D)
unnamed: U25.11 (O4), U86.12
unnamed: U28.11 (Clk), U64.3 (C), U65.6 (~Q)
unnamed: U34.4, U81.6
unnamed: U34.5, U79.8
unnamed: U36.2, U37.1, U40.12 (Q8)
unnamed: U36.3, U40.10 (CLK)
unnamed: U36.5, U37.3, U41.14 (Q9)
unnamed: U36.6, U41.10 (CLK)
unnamed: U37.4, U37.5
unnamed: U43.1 (A->B), U44.1 (E), U48.6
unnamed: U44.15 (E), U48.11
unnamed: U45.2 (Q0), U49.1
unnamed: U45.5 (Q1), U49.3
unnamed: U45.7 (Q2), U49.5
unnamed: U45.10 (Q3), U49.11
unnamed: U55.4, U55.8
unnamed: U55.6, U56.2 (D)
unnamed: U55.5, U55.11
unnamed: U56.8 (~Q), U56.10 (~S)
unnamed: U56.5 (Q), U56.12 (D)
unnamed: U58.8 (~Q), U61.1
unnamed: U58.11 (C), U59.3
unnamed: U58.13 (~R), U60.6 (~Q), U61.2
unnamed: U59.5, U60.9 (Q)
unnamed: U62.5 (Q), U86.2
unnamed: U64.4 (~S), U64.6 (~Q)
unnamed: U64.9 (Q), U65.2 (D)
unnamed: U78.9 (O6), U79.3
unnamed: U78.14 (O1), U79.1
unnamed: U80.2, U80.3
unnamed: U80.4, U80.5
unnamed: U80.6, U80.9
unnamed: U80.10, U81.12
unnamed: U80.11, U80.12
unnamed: U86.6, U86.9
unnamed: U87.14 (O1), U88.2
unnamed: U87.15 (O0), U88.1
unnamed: U88.3, U88.4
unnamed: U88.5, U88.8
unnamed: U89.3, U90.9
unnamed: U89.6, U90.10
unnamed: U89.9, U90.11
unnamed: U89.10, U89.11
unnamed: U90.3, U90.12
unnamed: U91.9 (RCLK), U91.15 (~BAUDOUT~)
unnamed: U95.2, U96.3 (C)
unnamed: U96.2 (D), U96.6 (~Q)
unnamed: U96.5 (Q), U96.11 (C)
unnamed: U96.8 (~Q), U96.12 (D)
unnamed: U97.50 (X1), Y5.1
unnamed: U97.51 (X2), Y5.2
unnamed: U97.76 (EECS), U98.1 (CS)
unnamed: U97.77 (PL1/EEDO), U98.4 (DO)
unnamed: U97.78 (IRQS0/EEDI), U98.3 (DI)
unnamed: U97.79 (IRQS1/EESK), U98.2 (SCLK)
ON_PULSE: D1.2 (A), U37.2, U39.3 (C)
OSC: J6.30 (OSC), J8.30 (OSC), J9.30 (OSC), J10.30 (OSC), J11.30 (OSC), J12.30 (OSC), J13.30 (OSC), R23.2, U21.1 (CP1..3), U62.3 (C), U99.49 (OSC)
PCLK: U21.8 (Q3), U21.14 (CP0), U64.11 (C), U65.3 (C)
PPI_PA0: U27.4 (PA0), U28.13 (H/Qh)
PPI_PA1: U27.3 (PA1), U28.7 (G/Qg)
PPI_PA2: U27.2 (PA2), U28.14 (F/Qf)
PPI_PA3: U27.1 (PA3), U28.6 (E/Qe)
PPI_PA4: U27.40 (PA4), U28.15 (D/Qd)
PPI_PA5: U27.39 (PA5), U28.5 (C/Qc)
PPI_PA6: U27.38 (PA6), U28.16 (B/Qb)
PPI_PA7: U27.37 (PA7), U28.4 (A/Qa)
PPI_PB2: RN4.2 (R1), U27.20 (PB2), U62.12 (D)
PPI_PB3: RN4.3 (R2), U27.21 (PB3), U29.1 (OEa), U66.1
PPI_PB4: RN4.4 (R3), U27.22 (PB4)
PPI_PB5: RN4.5 (R4), U27.23 (PB5)
PPI_PB6: U27.24 (PB6), U66.5
PPI_PB7: U27.25 (PB7), U28.8 (OE), U66.11
PPI_PC0: U27.14 (PC0), U29.9 (O0b), U29.18 (O0a)
PPI_PC1: U27.15 (PC1), U29.7 (O1b), U29.16 (O1a)
PPI_PC2: U27.16 (PC2), U29.5 (O2b), U29.14 (O2a)
PPI_PC3: U27.17 (PC3), U29.3 (O3b), U29.12 (O3a)
PPI_PC4: U27.13 (PC4)
QS0: U1.25 (QS0), U15.25 (QS0)
QS1: U1.24 (QS1), U15.24 (QS1)
RDY_TO_DMA: U22.6 (READY), U61.3
READY: U1.22 (READY), U15.22 (READY), U19.5 (READY)
RESET: U1.21 (RESET), U15.21 (RESET), U19.10 (RESET), U21.6 (R0(1)), U21.7 (R0(2)), U22.13 (RESET), U27.35 (RESET), U32.19 (RESET), U54.3, U99.24 (RESET)
RESETDRV: C98.2, J6.2 (RESET), J8.2 (RESET), J9.2 (RESET), J10.2 (RESET), J11.2 (RESET), J12.2 (RESET), J13.2 (RESET), U8.13 (B5), U97.33 (RESET)
RESETISA: U8.7 (A5), U54.6
ROM_P1: J2.2, R4.2, U12.2 (A16)
SCSI_ASEL0: J33.1, U99.10 (ASEL0)
SCSI_ASEL1: J33.3, U99.11 (ASEL1)
SCSI_ASEL2: J33.5, U99.12 (ASEL2)
SD0: U99.22 (D0), U100.18 (B0)
SD1: U99.21 (D1), U100.17 (B1)
SD2: U99.20 (D2), U100.16 (B2)
SD3: U99.19 (D3), U100.15 (B3)
SD4: U99.17 (D4), U100.14 (B4)
SD5: U99.16 (D5), U100.13 (B5)
SD6: U99.15 (D6), U100.12 (B6)
SD7: U99.14 (D7), U100.11 (B7)
SPKDATA: U27.19 (PB1), U88.13
TCLK: U21.12 (Q0), U26.9 (CLK0), U26.15 (CLK1), U26.18 (CLK2)
TERMPWR: C185.1, C186.1, F3.2, J36.26, R56.1, R58.1, RN7.1 (common), RN9.1 (common)
TIM1OUT: U26.13 (OUT1)
TIM2GSPK: U26.16 (G2), U27.18 (PB0)
TIM2OUT: U26.17 (OUT2), U27.12 (PC5), U88.12
TIMING_CLK: R35.2, U36.1, U36.4, U38.3 (Q)
TURBO: U19.13 (F/~C~), U62.9 (Q)
T_C: C120.2, J6.27 (TC), J8.27 (TC), J9.27 (TC), J10.27 (TC), J11.27 (TC), J12.27 (TC), J13.27 (TC), U32.6 (TC), U54.10
VCC: C30.1, C31.1, C32.1, C33.1, C34.1, C35.1, C36.1, C37.1, C38.1, C39.1, C40.1, C41.1, C42.1, C43.1, C44.1, C45.1, C46.1, C47.1, C48.1, C49.1, C50.1, C51.1, C52.1, C53.1, C54.1, C55.1, C56.1, C57.1, C58.1, C59.1, C60.1, C61.1, C62.1, C63.1, C64.1, C65.1, C66.1, C67.1, C68.1, C69.1, C70.1, C71.1, C72.1, C73.1, C74.1, C75.1, C76.1, C77.1, C79.1, C80.1, C81.1, C82.1, C83.1, C84.1, C85.1, C86.1, C89.1, C90.1, C91.1, C92.1, C93.1, C94.1, C95.1, C96.1, C97.1, C177.1, C178.1, C179.1, C180.1, C181.1, C183.1, C184.1, D4.2 (A), F1.1, FB1.2, J1.2, J1.4, J2.1, J6.3 (+5V), J6.29 (VCC), J6.78 (+5V), J8.3 (+5V), J8.29 (VCC), J8.78 (+5V), J9.3 (+5V), J9.29 (VCC), J9.78 (+5V), J10.3 (+5V), J10.29 (VCC), J10.78 (+5V), J11.3 (+5V), J11.29 (VCC), J11.78 (+5V), J12.3 (+5V), J12.29 (VCC), J12.78 (+5V), J13.3 (+5V), J13.29 (VCC), J13.78 (+5V), R16.1, R38.2, R42.2, R43.1, R44.1, R48.1, R49.1, R52.1, R53.1, RN1.1 (common), RN2.1 (common), RN3.1 (common), RN4.1 (common), RN5.1 (common), RN6.1 (common), RN11.1 (common), U1.40 (VCC), U2.20 (VCC), U3.20 (VCC), U4.20 (VCC), U5.20 (VCC), U6.20 (VCC), U7.1 (A->B), U7.20 (VCC), U8.1 (A->B), U8.20 (VCC), U9.20 (VCC), U10.20 (VCC), U12.32 (VCC), U13.32 (VCC), U14.32 (VCC), U15.33 (~RQ~/~GT1~), U15.34 (~BHE~/S7), U15.40 (VCC), U16.20 (VCC), U17.20 (VCC), U19.7 (~AEN2~), U19.18 (VCC), U20.14 (VCC), U21.5 (VCC), U22.5 (PIN5), U22.31 (Vcc), U23.16 (VCC), U24.20 (VCC), U25.16 (VCC), U26.11 (G0), U26.14 (G1), U26.24 (VCC), U27.26 (VCC), U28.2 (S/P), U28.3 (D0), U28.18 (SE), U28.19 (DS), U28.20 (VCC), U29.20 (VCC), U30.16 (~SP~/~EN~), U30.28 (VCC), U31.28 (VCC), U32.24 (PCVAL), U32.40 (VCC), U33.6 (E3), U33.16 (VCC), U34.9, U34.10, U34.13, U34.14 (VCC), U43.20 (VCC), U44.16 (VCC), U45.16 (VCC), U46.20 (VCC), U47.1 (A->B), U47.20 (VCC), U48.9, U48.10, U48.14 (VCC), U49.14 (VCC), U54.14 (VCC), U55.14 (VCC), U56.4 (~S), U56.14 (VCC), U58.4 (~S), U58.12 (D), U58.14 (VCC), U59.14 (VCC), U60.4 (~S), U60.10 (~S), U60.14 (VCC), U61.9, U61.10, U61.12, U61.13, U61.14 (VCC), U62.4 (~S), U62.10 (~S), U62.13 (~R), U62.14 (VCC), U64.10 (~S), U64.14 (VCC), U65.4 (~S), U65.10 (~S), U65.11 (C), U65.12 (D), U65.14 (VCC), U66.14 (VCC), U68.14 (VCC), U69.14 (VCC), U70.14 (VCC), U71.14 (VCC), U73.20 (VCC), U74.20 (VCC), U75.20 (VCC), U76.1 (A->B), U76.20 (VCC), U78.16 (VCC), U79.14 (VCC), U80.14 (VCC), U81.9, U81.10, U81.14 (VCC), U83.6 (E3), U83.16 (VCC), U84.6 (E3), U84.16 (VCC), U85.16 (VCC), U86.14 (VCC), U87.16 (VCC), U88.14 (VCC), U89.14 (VCC), U90.14 (VCC), U91.40 (VCC), U93.20 (VCC), U95.14 (VCC), U96.1 (~R), U96.4 (~S), U96.10 (~S), U96.13 (~R), U96.14 (VCC), U97.6 (VCC), U97.17 (VCC), U97.47 (VCC), U97.57 (VCC), U97.70 (VCC), U97.89 (VCC), U98.8 (VCC), U99.13 (VCC), U100.20 (VCC)
X7X: U91.13 (CS1), U95.10
XA0: U6.11 (B7), U12.12 (A0), U13.12 (A0), U14.12 (A0), U22.32 (A0), U23.14 (Wa), U26.19 (A0), U27.9 (A0), U30.27 (A0), U31.27 (A0)
XA1: U6.12 (B6), U12.11 (A1), U13.11 (A1), U14.11 (A1), U22.33 (A1), U23.13 (Wb), U26.20 (A1), U27.8 (A1)
XA2: U6.13 (B5), U12.10 (A2), U13.10 (A2), U14.10 (A2), U22.34 (A2)
XA3: U6.14 (B4), U12.9 (A3), U13.9 (A3), U14.9 (A3), U22.35 (A3)
XA4: U6.15 (B3), U12.8 (A4), U13.8 (A4), U14.8 (A4), U22.37 (A4), U48.2
XA5: U6.16 (B2), U12.7 (A5), U13.7 (A5), U14.7 (A5), U22.38 (A5), U25.1 (A0)
XA6: U6.17 (B1), U12.6 (A6), U13.6 (A6), U14.6 (A6), U22.39 (A6), U25.2 (A1)
XA7: U6.18 (B0), U12.5 (A7), U13.5 (A7), U14.5 (A7), U22.40 (A7), U25.3 (A2)
XA8: U7.11 (B7), U12.27 (A8), U13.27 (A8), U14.27 (A8), U25.5 (E2), U90.1
XA9: U7.12 (B6), U12.26 (A9), U13.26 (A9), U14.26 (A9), U25.4 (E1), U90.2
XA10: U7.13 (B5), U12.23 (A10), U13.23 (A10), U14.23 (A10)
XA11: U7.14 (B4), U12.25 (A11), U13.25 (A11), U14.25 (A11)
XA12: U7.15 (B3), U12.4 (A12), U13.4 (A12), U14.4 (A12)
XA13: U7.16 (B2), U12.28 (A13), U13.28 (A13), U14.28 (A13)
XA14: U7.17 (B1), U12.29 (A14), U13.3 (A14), U14.3 (A14)
XA15: U7.18 (B0), U12.3 (A15), U13.31 (A15), U14.31 (A15)
XA16: U8.18 (B0), U13.2 (A16), U14.2 (A16), U87.1 (A0)
XA17: U8.17 (B1), U13.30 (A17), U14.30 (A17), U87.2 (A1)
XA18: U8.16 (B2), U13.1 (A18), U14.1 (A18), U87.3 (A2)
XA19: U8.15 (B3), U13.22 (CE#), U87.6 (E3)
XD0: U9.18 (B0), U12.13 (D0), U22.30 (DB0), U23.15 (D1), U24.9 (D7), U26.8 (D0), U27.34 (D0), U30.11 (D0), U31.11 (D0)
XD1: U9.17 (B1), U12.14 (D1), U22.29 (DB1), U23.1 (D2), U24.8 (D6), U26.7 (D1), U27.33 (D1), U30.10 (D1), U31.10 (D1)
XD2: U9.16 (B2), U12.15 (D2), U22.28 (DB2), U23.2 (D3), U24.7 (D5), U26.6 (D2), U27.32 (D2), U30.9 (D2), U31.9 (D2)
XD3: U9.15 (B3), U12.17 (D3), U22.27 (DB3), U23.3 (D4), U24.6 (D4), U26.5 (D3), U27.31 (D3), U30.8 (D3), U31.8 (D3)
XD4: U9.14 (B4), U12.18 (D4), U22.26 (DB4), U24.5 (D3), U26.4 (D4), U27.30 (D4), U30.7 (D4), U31.7 (D4)
XD5: U9.13 (B5), U12.19 (D5), U22.23 (DB5), U24.4 (D2), U26.3 (D5), U27.29 (D5), U30.6 (D5), U31.6 (D5)
XD6: U9.12 (B6), U12.20 (D6), U22.22 (DB6), U24.3 (D1), U26.2 (D6), U27.28 (D6), U30.5 (D6), U31.5 (D6)
XD7: U9.11 (B7), U12.21 (D7), U22.21 (DB7), U24.2 (D0), U26.1 (D7), U27.27 (D7), U30.4 (D7), U31.4 (D7)
XD_DIR: U9.1 (A->B), U89.8
~00X: U83.15 (O0)
~06X: U25.12 (O3), U48.1
~08X: U83.14 (O1)
~10X: U83.13 (O2)
~18X: U83.12 (O3)
~20X: U83.11 (O4)
~28X: U83.10 (O5)
~30X: U81.1, U83.9 (O6), U86.4
~38X: U33.5 (E2), U83.7 (O7), U91.14 (~CS2~)
~A1: U78.6 (E3), U79.6
~AEN: J30.3, U16.15 (CEN), U25.6 (E3), U58.6 (~Q)
~BIDE_CS0: J21.37, U76.12 (B6)
~BIDE_CS1: J21.38, U76.11 (B7)
~BIOR: U32.1 (~RD), U48.4, U73.1 (A->B), U76.13 (B5), U78.2 (A1), U80.1, U81.4, U91.21 (~RD~), U97.29 (IOR)
~BIOW: J21.23, U32.2 (~WR), U48.12, U76.14 (B4), U78.1 (A0), U91.18 (~WR~), U97.30 (IOW)
~CLK: U54.8, U56.11 (C)
~COM1_CTS: U91.36 (~CTS~), U93.14 (RY4)
~COM1_DCD: U91.38 (~DCD~), U93.19 (RY1)
~COM1_DSR: U91.37 (~DSR~), U93.18 (RY2)
~COM1_DTR: U91.33 (~DTR~), U93.13 (DA3)
~COM1_RI: U91.39 (~RI~), U93.12 (RY5)
~COM1_RTS: U91.32 (~RTS~), U93.16 (DA1)
~DACK0: U8.9 (A7), U22.25 (DACK0)
~DACK1: C110.2, J6.17 (~DACK1), J8.17 (~DACK1), J9.17 (~DACK1), J10.17 (~DACK1), J11.17 (~DACK1), J12.17 (~DACK1), J13.17 (~DACK1), U22.24 (DACK1)
~DACK2: C119.2, J6.26 (~DACK2), J8.26 (~DACK2), J9.26 (~DACK2), J10.26 (~DACK2), J11.26 (~DACK2), J12.26 (~DACK2), J13.26 (~DACK2), U22.14 (DACK2), U23.4 (Rb), U32.5 (~DACK)
~DACK3: C108.2, J6.15 (~DACK3), J8.15 (~DACK3), J9.15 (~DACK3), J10.15 (~DACK3), J11.15 (~DACK3), J12.15 (~DACK3), J13.15 (~DACK3), U22.15 (DACK3), U23.5 (Ra)
~DC: J18.34, RN5.6 (R5), U79.9
~DEN: U5.19 (CE), U54.12
~DIR: J18.18, U32.28 (~DIRC)
~DMAAEN: J30.1, U17.1 (A->B), U23.11 (~Er), U24.1 (OE), U59.6, U61.5
~DMAWAIT: U19.4 (RDY1), U60.8 (~Q)
~DMA_CS: U22.11 (~CS~), U25.15 (O0)
~DSA: J18.14, U32.30 (~DS1)
~DSB: J18.12, U32.32 (~DS2)
~EOP: RN1.9 (R8), U22.36 (~EOP~), U54.11
~FDC_CS: U32.3 (~CS), U33.13 (O2)
~FDC_LDCR: U32.18 (~LDCR), U33.12 (O3), U81.5
~FDC_LDOR: U32.17 (~LDOR), U33.14 (O1)
~IDE_ACT: J21.39, U34.1
~IDE_CS: U73.19 (CE), U78.4 (E1), U81.3, U85.15 (E)
~IDE_CS0: U76.8 (A6), U85.12 (O0)
~IDE_CS1: U76.9 (A7), U85.11 (O1)
~IDE_DMACK: J21.29, R38.1
~IDE_DMARQ: J21.21, R39.1
~IDX: J18.8, RN5.2 (R1), U32.39 (~IDX)
~INT1_CS: U25.14 (O1), U30.1 (~CS~)
~INT2_CS: U25.10 (O5), U31.1 (~CS~)
~INTA: RN1.7 (R6), U16.14 (~INTA~), U30.26 (~INTA~), U31.26 (~INTA~), U89.13
~IOR: C107.2, J6.14 (~IOR), J8.14 (~IOR), J9.14 (~IOR), J10.14 (~IOR), J11.14 (~IOR), J12.14 (~IOR), J13.14 (~IOR), RN1.5 (R4), U16.13 (~IORC~), U17.5 (A3), U76.7 (A5)
~IOR_DLY: J21.25, U80.8
~IOW: C106.2, J6.13 (~IOW), J8.13 (~IOW), J9.13 (~IOW), J10.13 (~IOW), J11.13 (~IOW), J12.13 (~IOW), J13.13 (~IOW), RN1.3 (R2), U16.12 (~AIOWC~), U17.3 (A1), U76.6 (A4), U99.48 (~IOW)
~KB_RESET: C5.1, R21.1, U70.3
~LOCK: U1.29 (~LOCK~), U55.9
~LPT_ACK: J20.10, U69.12, U71.1
~LPT_AUTO_FD_XT: J20.14, RN6.6 (R5), U49.4, U71.5
~LPT_BUSY: U70.12, U71.12
~LPT_CS: U48.5, U48.13, U86.8
~LPT_ERROR: J20.15, U68.5
~LPT_INIT: J20.16, RN6.5 (R4), U49.12, U69.9
~LPT_IRQ_EN: RN6.3 (R2), U49.8, U70.4
~LPT_RD_A: U44.4 (O0), U47.19 (CE)
~LPT_RD_B: U44.5 (O1), U68.4, U68.10, U68.13, U69.13, U70.13
~LPT_RD_C: U44.6 (O2), U68.1, U69.1, U69.4, U69.10, U70.10
~LPT_SELECT_IN: J20.17, RN6.9 (R8), U49.10, U71.11
~LPT_STROBE: C29.1, J20.1, RN6.7 (R6), U49.2, U71.3
~LPT_WR_A: U44.12 (O0), U46.11 (Cp)
~LPT_WR_C: U44.10 (O2), U45.9 (Cp)
~MEMR: C104.2, J6.12 (~SMEMR), J8.12 (~SMEMR), J9.12 (~SMEMR), J10.12 (~SMEMR), J11.12 (~SMEMR), J12.12 (~SMEMR), J13.12 (~SMEMR), RN1.2 (R1), U16.7 (~MRDC~), U17.2 (A0), U97.31 (MEMR), U99.46 (~SMEMR), U100.1 (A->B)
~MEMW: C103.2, J6.11 (~SMEMW), J8.11 (~SMEMW), J9.11 (~SMEMW), J10.11 (~SMEMW), J11.11 (~SMEMW), J12.11 (~SMEMW), J13.11 (~SMEMW), RN1.4 (R3), U16.8 (~AMWC~), U17.4 (A2), U97.32 (MEMW), U99.47 (~SMEMW)
~MOTEA: J18.10, U32.33 (~MO1~_~DS3)
~MOTEB: J18.16, U32.34 (~MO2~_~DS4)
~MR: C167.2, J6.89 (~MEMR), J8.89 (~MEMR), J9.89 (~MEMR), J10.89 (~MEMR), J11.89 (~MEMR), J12.89 (~MEMR), J13.89 (~MEMR)
~MW: C168.2, J6.90 (~MEMW), J8.90 (~MEMW), J9.90 (~MEMW), J10.90 (~MEMW), J11.90 (~MEMW), J12.90 (~MEMW), J13.90 (~MEMW)
~MWTC: RN1.6 (R5), U16.9 (~MWTC~)
~OE_RD_H: U75.1 (OE), U78.10 (O5)
~OE_WR_H: U78.13 (O2), U80.13
~OE_WR_H_DLY: U74.1 (OE), U81.11
~PPI_CS: U27.6 (~CS~), U48.3
~PPI_PB3: RN4.6 (R5), U29.19 (OEb), U66.2
~PPI_PB6: RN4.7 (R6), U66.6, U66.9
~PPI_PB7: RN4.8 (R7), U28.9 (Clr), U64.1 (~R), U66.10
~RAMCS1: U14.22 (CE#), U88.6, U89.5
~RAM_ACT: U10.19 (CE), U90.8
~RDD: J18.30, RN5.5 (R4), U32.20 (~RDD)
~RDY~_WAIT: U19.3 (~AEN1~), U58.9 (Q), U60.2 (D)
~REFRESH: C112.2, J6.19 (~REFRESH), J8.19 (~REFRESH), J9.19 (~REFRESH), J10.19 (~REFRESH), J11.19 (~REFRESH), J12.19 (~REFRESH), J13.19 (~REFRESH), U8.11 (B7)
~RES: U19.11 (~RES~), U37.6
~RESET: J21.1, U45.1 (~Mr), U54.4, U54.5, U56.1 (~R), U58.1 (~R), U60.1 (~R), U60.13 (~R), U62.1 (~R), U64.13 (~R), U65.1 (~R), U70.2
~ROMCS: U12.22 (CE), U87.7 (O7), U90.4
~ROM_RD: U89.12, U90.6
~RQ_GT: U1.30 (~RQ~/~GT1~), U15.31 (~RQ~/~GT0~)
~S0: U1.26 (~S0~), U15.26 (~S0~), U16.19 (~S0~), U55.10
~S1: U1.27 (~S1~), U15.27 (~S1~), U16.3 (~S1~), U55.12
~S2: U1.28 (~S2~), U15.28 (~S2~), U16.18 (~S2~)
~SCSI_ACK: J36.38, RN9.5 (R4), RN10.5 (R4), U99.57 (~SACK)
~SCSI_ATN: J36.32, RN9.3 (R2), RN10.3 (R2), U99.60 (~SATN)
~SCSI_BSY: J36.36, RN9.4 (R3), RN10.4 (R3), U99.59 (~SBSY)
~SCSI_CD: J36.46, RN9.9 (R8), RN10.9 (R8), U99.53 (~SC_D)
~SCSI_DB0: J36.2, RN7.2 (R1), RN8.2 (R1), U99.3 (~SDB0)
~SCSI_DB1: J36.4, RN7.3 (R2), RN8.3 (R2), U99.2 (~SDB1)
~SCSI_DB2: J36.6, RN7.4 (R3), RN8.4 (R3), U99.68 (~SDB2)
~SCSI_DB3: J36.8, RN7.5 (R4), RN8.5 (R4), U99.67 (~SDB3)
~SCSI_DB4: J36.10, RN7.6 (R5), RN8.6 (R5), U99.66 (~SDB4)
~SCSI_DB5: J36.12, RN7.7 (R6), RN8.7 (R6), U99.65 (~SDB5)
~SCSI_DB6: J36.14, RN7.8 (R7), RN8.8 (R7), U99.63 (~SDB6)
~SCSI_DB7: J36.16, RN7.9 (R8), RN8.9 (R8), U99.62 (~SDB7)
~SCSI_DBP: J36.18, RN9.2 (R1), RN10.2 (R1), U99.61 (~SDBP)
~SCSI_IO: J36.50, R58.2, R59.2, U99.50 (~SIO)
~SCSI_MSG: J36.42, RN9.7 (R6), RN10.7 (R6), U99.55 (~SMSG)
~SCSI_REQ: J36.48, R56.2, R57.2, U99.51 (~SREQ)
~SCSI_RST: J36.40, RN9.6 (R5), RN10.6 (R5), U99.56 (~SRST)
~SCSI_SEL: J36.44, RN9.8 (R7), RN10.8 (R7), U99.54 (~SSEL)
~SDRV_SEL: U99.7 (~DRV_SEL), U100.19 (CE)
~SIDE: J18.32, U32.25 (~HS)
~STEP: J18.20, U32.29 (~STEP)
~TEST: R48.2, U1.23 (~TEST~), U15.23 (BUSY)
~TMR_CS: U25.13 (O2), U26.21 (~CS~)
~TR0: J18.26, RN5.3 (R2), U32.38 (~TR00)
~WDATA: J18.22, U32.27 (~WD)
~WGATE: J18.24, U32.26 (~WE)
~WP: J18.28, RN5.4 (R3), U32.37 (~WP)
~WRTDMAPREG: U23.12 (~Ew), U86.11
~X0X: U81.2, U84.15 (O0)
~X1X: U84.14 (O1)
~X2X: U84.13 (O2)
~X3X: U84.12 (O3)
~X4X: U84.11 (O4)
~X5X: U84.10 (O5)
~X6X: U84.9 (O6)
~X7X: U33.4 (E1), U84.7 (O7), U86.5, U95.11
~XEN: J31.1, U61.6
~XIOR: RN3.5 (R4), U17.15 (B3), U22.1 (~IOR~), U26.22 (~RD~), U27.5 (~RD~), U30.3 (~RD~), U31.3 (~RD~), U59.1, U90.13
~XIOW: RN3.3 (R2), U17.17 (B1), U22.2 (~IOW~), U26.23 (~WR~), U27.36 (~WR~), U30.2 (~WR~), U31.2 (~WR~), U59.2, U86.13
~XMEMR: RN3.2 (R1), U10.1 (A->B), U12.24 (OE), U13.24 (OE#), U14.24 (OE#), U17.18 (B0), U22.3 (~MEMR~), U89.1, U90.5
~XMEMW: RN3.4 (R3), U12.31 (PGM), U13.29 (WE#), U14.29 (WE#), U17.16 (B2), U22.4 (~MEMW~), U89.2
~XX0: U78.5 (E2), U85.4 (O0)
~XX4: U85.5 (O1)
~XX8: U85.6 (O2), U86.10
~XXC: U85.7 (O3)

Notes on the sheet:
XBUS DATA DIRECTIONAL CONTROL
OPEN =PAGE0 (LOWER) CLOSED = PAGE1 (UPPER)
14.31818M
4.77M / 8M
4.773 Mhz
2.386 Mhz
1.193 Mhz
14.31818 Mhz
SYSTEM TIMER
TURBO LED
XT KEYBOARD
FLOPPY DRIVE CONNECTOR
FLOPPY DRIVE CONTROLLER
POWER SWITCH
STANDBY POWER LED
LPT IRQ ENABLE
LPT
FDC
3F2
3F4
3F7
(IDE_A0)
PORT 300-30F
LED YEL
HIGH SPEED MODE
TOP(8k PAGES): XTBIOS XT-IDE XT-HD FDD
XT-IDE
PORT 378-37B
SEGMENT D0000 - 64kb RAM
SEGMENT E0000 - 64kb RAM
COM1
COM PORT
UMB 1:
UMB 2:
RAM DATA BUS ENABLE
RAM 2 AND ROM DECODER
I/O DECODING
DMA BUS CONTROL, I/O WAIT STATES
POWER & RESET
RESET SWITCH
DMA TIMING OPTIONS
DEFAULT: ~XEN
DEFAULT: ~DMAAEN
ETHERNET
SCSI
SCSI ADDRESS DEFAULT = C800 1-2 OFF 3-4 OFF 5-6 ON
OPTION: FIXED CAP
OR SST39SF010
DO NOT USE UNLESS BIOS IS SUITABLE
(CONNECTOR)
PROJECT DESIGNED AND TESTED BY RODNEY KNAAP (2023) https://github.com/rodneyknaap/atx-turboxt-v3/tree/main https://www.knaapic.nl/wordpress/1063-2
